Carlo910/ReHand-Project/Eagle/c.png

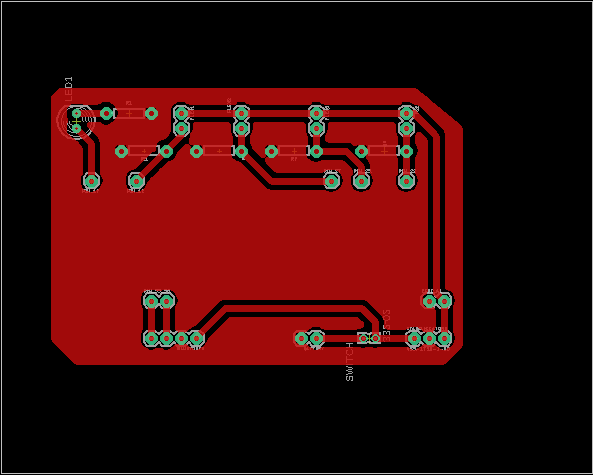
Eagle/c.png
