Carlo910/ReHand-Project/PYTHON/Immagini/indice_medio.png

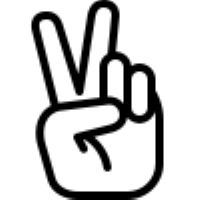
PYTHON/Immagini/indice_medio.png
