Carlo910/ReHand-Project/PSOC/Project3.cydsn/codegentemp/UART_BT.c

/*******************************************************************************
* File Name: UART_BT.c
* Version 2.50
*
* Description:
*  This file provides all API functionality of the UART component
*
* Note:
*
********************************************************************************
* Copyright 2008-2015, Cypress Semiconductor Corporation.  All rights reserved.
* You may use this file only in accordance with the license, terms, conditions,
* disclaimers, and limitations in the end user license agreement accompanying
* the software package with which this file was provided.
*******************************************************************************/

#include "UART_BT.h"
#if (UART_BT_INTERNAL_CLOCK_USED)
    #include "UART_BT_IntClock.h"
#endif /* End UART_BT_INTERNAL_CLOCK_USED */


/***************************************
* Global data allocation
***************************************/

uint8 UART_BT_initVar = 0u;

#if (UART_BT_TX_INTERRUPT_ENABLED && UART_BT_TX_ENABLED)
    volatile uint8 UART_BT_txBuffer[UART_BT_TX_BUFFER_SIZE];
    volatile uint8 UART_BT_txBufferRead = 0u;
    uint8 UART_BT_txBufferWrite = 0u;
#endif /* (UART_BT_TX_INTERRUPT_ENABLED && UART_BT_TX_ENABLED) */

#if (UART_BT_RX_INTERRUPT_ENABLED && (UART_BT_RX_ENABLED || UART_BT_HD_ENABLED))
    uint8 UART_BT_errorStatus = 0u;
    volatile uint8 UART_BT_rxBuffer[UART_BT_RX_BUFFER_SIZE];
    volatile uint8 UART_BT_rxBufferRead  = 0u;
    volatile uint8 UART_BT_rxBufferWrite = 0u;
    volatile uint8 UART_BT_rxBufferLoopDetect = 0u;
    volatile uint8 UART_BT_rxBufferOverflow   = 0u;
    #if (UART_BT_RXHW_ADDRESS_ENABLED)
        volatile uint8 UART_BT_rxAddressMode = UART_BT_RX_ADDRESS_MODE;
        volatile uint8 UART_BT_rxAddressDetected = 0u;
    #endif /* (UART_BT_RXHW_ADDRESS_ENABLED) */
#endif /* (UART_BT_RX_INTERRUPT_ENABLED && (UART_BT_RX_ENABLED || UART_BT_HD_ENABLED)) */


/*******************************************************************************
* Function Name: UART_BT_Start
********************************************************************************
*
* Summary:
*  This is the preferred method to begin component operation.
*  UART_BT_Start() sets the initVar variable, calls the
*  UART_BT_Init() function, and then calls the
*  UART_BT_Enable() function.
*
* Parameters:
*  None.
*
* Return:
*  None.
*
* Global variables:
*  The UART_BT_intiVar variable is used to indicate initial
*  configuration of this component. The variable is initialized to zero (0u)
*  and set to one (1u) the first time UART_BT_Start() is called. This
*  allows for component initialization without re-initialization in all
*  subsequent calls to the UART_BT_Start() routine.
*
* Reentrant:
*  No.
*
*******************************************************************************/
void UART_BT_Start(void) 
{
    /* If not initialized then initialize all required hardware and software */
    if(UART_BT_initVar == 0u)
    {
        UART_BT_Init();
        UART_BT_initVar = 1u;
    }

    UART_BT_Enable();
}


/*******************************************************************************
* Function Name: UART_BT_Init
********************************************************************************
*
* Summary:
*  Initializes or restores the component according to the customizer Configure
*  dialog settings. It is not necessary to call UART_BT_Init() because
*  the UART_BT_Start() API calls this function and is the preferred
*  method to begin component operation.
*
* Parameters:
*  None.
*
* Return:
*  None.
*
*******************************************************************************/
void UART_BT_Init(void) 
{
    #if(UART_BT_RX_ENABLED || UART_BT_HD_ENABLED)

        #if (UART_BT_RX_INTERRUPT_ENABLED)
            /* Set RX interrupt vector and priority */
            (void) CyIntSetVector(UART_BT_RX_VECT_NUM, &UART_BT_RXISR);
            CyIntSetPriority(UART_BT_RX_VECT_NUM, UART_BT_RX_PRIOR_NUM);
            UART_BT_errorStatus = 0u;
        #endif /* (UART_BT_RX_INTERRUPT_ENABLED) */

        #if (UART_BT_RXHW_ADDRESS_ENABLED)
            UART_BT_SetRxAddressMode(UART_BT_RX_ADDRESS_MODE);
            UART_BT_SetRxAddress1(UART_BT_RX_HW_ADDRESS1);
            UART_BT_SetRxAddress2(UART_BT_RX_HW_ADDRESS2);
        #endif /* End UART_BT_RXHW_ADDRESS_ENABLED */

        /* Init Count7 period */
        UART_BT_RXBITCTR_PERIOD_REG = UART_BT_RXBITCTR_INIT;
        /* Configure the Initial RX interrupt mask */
        UART_BT_RXSTATUS_MASK_REG  = UART_BT_INIT_RX_INTERRUPTS_MASK;
    #endif /* End UART_BT_RX_ENABLED || UART_BT_HD_ENABLED*/

    #if(UART_BT_TX_ENABLED)
        #if (UART_BT_TX_INTERRUPT_ENABLED)
            /* Set TX interrupt vector and priority */
            (void) CyIntSetVector(UART_BT_TX_VECT_NUM, &UART_BT_TXISR);
            CyIntSetPriority(UART_BT_TX_VECT_NUM, UART_BT_TX_PRIOR_NUM);
        #endif /* (UART_BT_TX_INTERRUPT_ENABLED) */

        /* Write Counter Value for TX Bit Clk Generator*/
        #if (UART_BT_TXCLKGEN_DP)
            UART_BT_TXBITCLKGEN_CTR_REG = UART_BT_BIT_CENTER;
            UART_BT_TXBITCLKTX_COMPLETE_REG = ((UART_BT_NUMBER_OF_DATA_BITS +
                        UART_BT_NUMBER_OF_START_BIT) * UART_BT_OVER_SAMPLE_COUNT) - 1u;
        #else
            UART_BT_TXBITCTR_PERIOD_REG = ((UART_BT_NUMBER_OF_DATA_BITS +
                        UART_BT_NUMBER_OF_START_BIT) * UART_BT_OVER_SAMPLE_8) - 1u;
        #endif /* End UART_BT_TXCLKGEN_DP */

        /* Configure the Initial TX interrupt mask */
        #if (UART_BT_TX_INTERRUPT_ENABLED)
            UART_BT_TXSTATUS_MASK_REG = UART_BT_TX_STS_FIFO_EMPTY;
        #else
            UART_BT_TXSTATUS_MASK_REG = UART_BT_INIT_TX_INTERRUPTS_MASK;
        #endif /*End UART_BT_TX_INTERRUPT_ENABLED*/

    #endif /* End UART_BT_TX_ENABLED */

    #if(UART_BT_PARITY_TYPE_SW)  /* Write Parity to Control Register */
        UART_BT_WriteControlRegister( \
            (UART_BT_ReadControlRegister() & (uint8)~UART_BT_CTRL_PARITY_TYPE_MASK) | \
            (uint8)(UART_BT_PARITY_TYPE << UART_BT_CTRL_PARITY_TYPE0_SHIFT) );
    #endif /* End UART_BT_PARITY_TYPE_SW */
}


/*******************************************************************************
* Function Name: UART_BT_Enable
********************************************************************************
*
* Summary:
*  Activates the hardware and begins component operation. It is not necessary
*  to call UART_BT_Enable() because the UART_BT_Start() API
*  calls this function, which is the preferred method to begin component
*  operation.

* Parameters:
*  None.
*
* Return:
*  None.
*
* Global Variables:
*  UART_BT_rxAddressDetected - set to initial state (0).
*
*******************************************************************************/
void UART_BT_Enable(void) 
{
    uint8 enableInterrupts;
    enableInterrupts = CyEnterCriticalSection();

    #if (UART_BT_RX_ENABLED || UART_BT_HD_ENABLED)
        /* RX Counter (Count7) Enable */
        UART_BT_RXBITCTR_CONTROL_REG |= UART_BT_CNTR_ENABLE;

        /* Enable the RX Interrupt */
        UART_BT_RXSTATUS_ACTL_REG  |= UART_BT_INT_ENABLE;

        #if (UART_BT_RX_INTERRUPT_ENABLED)
            UART_BT_EnableRxInt();

            #if (UART_BT_RXHW_ADDRESS_ENABLED)
                UART_BT_rxAddressDetected = 0u;
            #endif /* (UART_BT_RXHW_ADDRESS_ENABLED) */
        #endif /* (UART_BT_RX_INTERRUPT_ENABLED) */
    #endif /* (UART_BT_RX_ENABLED || UART_BT_HD_ENABLED) */

    #if(UART_BT_TX_ENABLED)
        /* TX Counter (DP/Count7) Enable */
        #if(!UART_BT_TXCLKGEN_DP)
            UART_BT_TXBITCTR_CONTROL_REG |= UART_BT_CNTR_ENABLE;
        #endif /* End UART_BT_TXCLKGEN_DP */

        /* Enable the TX Interrupt */
        UART_BT_TXSTATUS_ACTL_REG |= UART_BT_INT_ENABLE;
        #if (UART_BT_TX_INTERRUPT_ENABLED)
            UART_BT_ClearPendingTxInt(); /* Clear history of TX_NOT_EMPTY */
            UART_BT_EnableTxInt();
        #endif /* (UART_BT_TX_INTERRUPT_ENABLED) */
     #endif /* (UART_BT_TX_INTERRUPT_ENABLED) */

    #if (UART_BT_INTERNAL_CLOCK_USED)
        UART_BT_IntClock_Start();  /* Enable the clock */
    #endif /* (UART_BT_INTERNAL_CLOCK_USED) */

    CyExitCriticalSection(enableInterrupts);
}


/*******************************************************************************
* Function Name: UART_BT_Stop
********************************************************************************
*
* Summary:
*  Disables the UART operation.
*
* Parameters:
*  None.
*
* Return:
*  None.
*
*******************************************************************************/
void UART_BT_Stop(void) 
{
    uint8 enableInterrupts;
    enableInterrupts = CyEnterCriticalSection();

    /* Write Bit Counter Disable */
    #if (UART_BT_RX_ENABLED || UART_BT_HD_ENABLED)
        UART_BT_RXBITCTR_CONTROL_REG &= (uint8) ~UART_BT_CNTR_ENABLE;
    #endif /* (UART_BT_RX_ENABLED || UART_BT_HD_ENABLED) */

    #if (UART_BT_TX_ENABLED)
        #if(!UART_BT_TXCLKGEN_DP)
            UART_BT_TXBITCTR_CONTROL_REG &= (uint8) ~UART_BT_CNTR_ENABLE;
        #endif /* (!UART_BT_TXCLKGEN_DP) */
    #endif /* (UART_BT_TX_ENABLED) */

    #if (UART_BT_INTERNAL_CLOCK_USED)
        UART_BT_IntClock_Stop();   /* Disable the clock */
    #endif /* (UART_BT_INTERNAL_CLOCK_USED) */

    /* Disable internal interrupt component */
    #if (UART_BT_RX_ENABLED || UART_BT_HD_ENABLED)
        UART_BT_RXSTATUS_ACTL_REG  &= (uint8) ~UART_BT_INT_ENABLE;

        #if (UART_BT_RX_INTERRUPT_ENABLED)
            UART_BT_DisableRxInt();
        #endif /* (UART_BT_RX_INTERRUPT_ENABLED) */
    #endif /* (UART_BT_RX_ENABLED || UART_BT_HD_ENABLED) */

    #if (UART_BT_TX_ENABLED)
        UART_BT_TXSTATUS_ACTL_REG &= (uint8) ~UART_BT_INT_ENABLE;

        #if (UART_BT_TX_INTERRUPT_ENABLED)
            UART_BT_DisableTxInt();
        #endif /* (UART_BT_TX_INTERRUPT_ENABLED) */
    #endif /* (UART_BT_TX_ENABLED) */

    CyExitCriticalSection(enableInterrupts);
}


/*******************************************************************************
* Function Name: UART_BT_ReadControlRegister
********************************************************************************
*
* Summary:
*  Returns the current value of the control register.
*
* Parameters:
*  None.
*
* Return:
*  Contents of the control register.
*
*******************************************************************************/
uint8 UART_BT_ReadControlRegister(void) 
{
    #if (UART_BT_CONTROL_REG_REMOVED)
        return(0u);
    #else
        return(UART_BT_CONTROL_REG);
    #endif /* (UART_BT_CONTROL_REG_REMOVED) */
}


/*******************************************************************************
* Function Name: UART_BT_WriteControlRegister
********************************************************************************
*
* Summary:
*  Writes an 8-bit value into the control register
*
* Parameters:
*  control:  control register value
*
* Return:
*  None.
*
*******************************************************************************/
void  UART_BT_WriteControlRegister(uint8 control) 
{
    #if (UART_BT_CONTROL_REG_REMOVED)
        if(0u != control)
        {
            /* Suppress compiler warning */
        }
    #else
       UART_BT_CONTROL_REG = control;
    #endif /* (UART_BT_CONTROL_REG_REMOVED) */
}


#if(UART_BT_RX_ENABLED || UART_BT_HD_ENABLED)
    /*******************************************************************************
    * Function Name: UART_BT_SetRxInterruptMode
    ********************************************************************************
    *
    * Summary:
    *  Configures the RX interrupt sources enabled.
    *
    * Parameters:
    *  IntSrc:  Bit field containing the RX interrupts to enable. Based on the 
    *  bit-field arrangement of the status register. This value must be a 
    *  combination of status register bit-masks shown below:
    *      UART_BT_RX_STS_FIFO_NOTEMPTY    Interrupt on byte received.
    *      UART_BT_RX_STS_PAR_ERROR        Interrupt on parity error.
    *      UART_BT_RX_STS_STOP_ERROR       Interrupt on stop error.
    *      UART_BT_RX_STS_BREAK            Interrupt on break.
    *      UART_BT_RX_STS_OVERRUN          Interrupt on overrun error.
    *      UART_BT_RX_STS_ADDR_MATCH       Interrupt on address match.
    *      UART_BT_RX_STS_MRKSPC           Interrupt on address detect.
    *
    * Return:
    *  None.
    *
    * Theory:
    *  Enables the output of specific status bits to the interrupt controller
    *
    *******************************************************************************/
    void UART_BT_SetRxInterruptMode(uint8 intSrc) 
    {
        UART_BT_RXSTATUS_MASK_REG  = intSrc;
    }


    /*******************************************************************************
    * Function Name: UART_BT_ReadRxData
    ********************************************************************************
    *
    * Summary:
    *  Returns the next byte of received data. This function returns data without
    *  checking the status. You must check the status separately.
    *
    * Parameters:
    *  None.
    *
    * Return:
    *  Received data from RX register
    *
    * Global Variables:
    *  UART_BT_rxBuffer - RAM buffer pointer for save received data.
    *  UART_BT_rxBufferWrite - cyclic index for write to rxBuffer,
    *     checked to identify new data.
    *  UART_BT_rxBufferRead - cyclic index for read from rxBuffer,
    *     incremented after each byte has been read from buffer.
    *  UART_BT_rxBufferLoopDetect - cleared if loop condition was detected
    *     in RX ISR.
    *
    * Reentrant:
    *  No.
    *
    *******************************************************************************/
    uint8 UART_BT_ReadRxData(void) 
    {
        uint8 rxData;

    #if (UART_BT_RX_INTERRUPT_ENABLED)

        uint8 locRxBufferRead;
        uint8 locRxBufferWrite;

        /* Protect variables that could change on interrupt */
        UART_BT_DisableRxInt();

        locRxBufferRead  = UART_BT_rxBufferRead;
        locRxBufferWrite = UART_BT_rxBufferWrite;

        if( (UART_BT_rxBufferLoopDetect != 0u) || (locRxBufferRead != locRxBufferWrite) )
        {
            rxData = UART_BT_rxBuffer[locRxBufferRead];
            locRxBufferRead++;

            if(locRxBufferRead >= UART_BT_RX_BUFFER_SIZE)
            {
                locRxBufferRead = 0u;
            }
            /* Update the real pointer */
            UART_BT_rxBufferRead = locRxBufferRead;

            if(UART_BT_rxBufferLoopDetect != 0u)
            {
                UART_BT_rxBufferLoopDetect = 0u;
                #if ((UART_BT_RX_INTERRUPT_ENABLED) && (UART_BT_FLOW_CONTROL != 0u))
                    /* When Hardware Flow Control selected - return RX mask */
                    #if( UART_BT_HD_ENABLED )
                        if((UART_BT_CONTROL_REG & UART_BT_CTRL_HD_SEND) == 0u)
                        {   /* In Half duplex mode return RX mask only in RX
                            *  configuration set, otherwise
                            *  mask will be returned in LoadRxConfig() API.
                            */
                            UART_BT_RXSTATUS_MASK_REG  |= UART_BT_RX_STS_FIFO_NOTEMPTY;
                        }
                    #else
                        UART_BT_RXSTATUS_MASK_REG  |= UART_BT_RX_STS_FIFO_NOTEMPTY;
                    #endif /* end UART_BT_HD_ENABLED */
                #endif /* ((UART_BT_RX_INTERRUPT_ENABLED) && (UART_BT_FLOW_CONTROL != 0u)) */
            }
        }
        else
        {   /* Needs to check status for RX_STS_FIFO_NOTEMPTY bit */
            rxData = UART_BT_RXDATA_REG;
        }

        UART_BT_EnableRxInt();

    #else

        /* Needs to check status for RX_STS_FIFO_NOTEMPTY bit */
        rxData = UART_BT_RXDATA_REG;

    #endif /* (UART_BT_RX_INTERRUPT_ENABLED) */

        return(rxData);
    }


    /*******************************************************************************
    * Function Name: UART_BT_ReadRxStatus
    ********************************************************************************
    *
    * Summary:
    *  Returns the current state of the receiver status register and the software
    *  buffer overflow status.
    *
    * Parameters:
    *  None.
    *
    * Return:
    *  Current state of the status register.
    *
    * Side Effect:
    *  All status register bits are clear-on-read except
    *  UART_BT_RX_STS_FIFO_NOTEMPTY.
    *  UART_BT_RX_STS_FIFO_NOTEMPTY clears immediately after RX data
    *  register read.
    *
    * Global Variables:
    *  UART_BT_rxBufferOverflow - used to indicate overload condition.
    *   It set to one in RX interrupt when there isn't free space in
    *   UART_BT_rxBufferRead to write new data. This condition returned
    *   and cleared to zero by this API as an
    *   UART_BT_RX_STS_SOFT_BUFF_OVER bit along with RX Status register
    *   bits.
    *
    *******************************************************************************/
    uint8 UART_BT_ReadRxStatus(void) 
    {
        uint8 status;

        status = UART_BT_RXSTATUS_REG & UART_BT_RX_HW_MASK;

    #if (UART_BT_RX_INTERRUPT_ENABLED)
        if(UART_BT_rxBufferOverflow != 0u)
        {
            status |= UART_BT_RX_STS_SOFT_BUFF_OVER;
            UART_BT_rxBufferOverflow = 0u;
        }
    #endif /* (UART_BT_RX_INTERRUPT_ENABLED) */

        return(status);
    }


    /*******************************************************************************
    * Function Name: UART_BT_GetChar
    ********************************************************************************
    *
    * Summary:
    *  Returns the last received byte of data. UART_BT_GetChar() is
    *  designed for ASCII characters and returns a uint8 where 1 to 255 are values
    *  for valid characters and 0 indicates an error occurred or no data is present.
    *
    * Parameters:
    *  None.
    *
    * Return:
    *  Character read from UART RX buffer. ASCII characters from 1 to 255 are valid.
    *  A returned zero signifies an error condition or no data available.
    *
    * Global Variables:
    *  UART_BT_rxBuffer - RAM buffer pointer for save received data.
    *  UART_BT_rxBufferWrite - cyclic index for write to rxBuffer,
    *     checked to identify new data.
    *  UART_BT_rxBufferRead - cyclic index for read from rxBuffer,
    *     incremented after each byte has been read from buffer.
    *  UART_BT_rxBufferLoopDetect - cleared if loop condition was detected
    *     in RX ISR.
    *
    * Reentrant:
    *  No.
    *
    *******************************************************************************/
    uint8 UART_BT_GetChar(void) 
    {
        uint8 rxData = 0u;
        uint8 rxStatus;

    #if (UART_BT_RX_INTERRUPT_ENABLED)
        uint8 locRxBufferRead;
        uint8 locRxBufferWrite;

        /* Protect variables that could change on interrupt */
        UART_BT_DisableRxInt();

        locRxBufferRead  = UART_BT_rxBufferRead;
        locRxBufferWrite = UART_BT_rxBufferWrite;

        if( (UART_BT_rxBufferLoopDetect != 0u) || (locRxBufferRead != locRxBufferWrite) )
        {
            rxData = UART_BT_rxBuffer[locRxBufferRead];
            locRxBufferRead++;
            if(locRxBufferRead >= UART_BT_RX_BUFFER_SIZE)
            {
                locRxBufferRead = 0u;
            }
            /* Update the real pointer */
            UART_BT_rxBufferRead = locRxBufferRead;

            if(UART_BT_rxBufferLoopDetect != 0u)
            {
                UART_BT_rxBufferLoopDetect = 0u;
                #if( (UART_BT_RX_INTERRUPT_ENABLED) && (UART_BT_FLOW_CONTROL != 0u) )
                    /* When Hardware Flow Control selected - return RX mask */
                    #if( UART_BT_HD_ENABLED )
                        if((UART_BT_CONTROL_REG & UART_BT_CTRL_HD_SEND) == 0u)
                        {   /* In Half duplex mode return RX mask only if
                            *  RX configuration set, otherwise
                            *  mask will be returned in LoadRxConfig() API.
                            */
                            UART_BT_RXSTATUS_MASK_REG |= UART_BT_RX_STS_FIFO_NOTEMPTY;
                        }
                    #else
                        UART_BT_RXSTATUS_MASK_REG |= UART_BT_RX_STS_FIFO_NOTEMPTY;
                    #endif /* end UART_BT_HD_ENABLED */
                #endif /* UART_BT_RX_INTERRUPT_ENABLED and Hardware flow control*/
            }

        }
        else
        {   rxStatus = UART_BT_RXSTATUS_REG;
            if((rxStatus & UART_BT_RX_STS_FIFO_NOTEMPTY) != 0u)
            {   /* Read received data from FIFO */
                rxData = UART_BT_RXDATA_REG;
                /*Check status on error*/
                if((rxStatus & (UART_BT_RX_STS_BREAK | UART_BT_RX_STS_PAR_ERROR |
                                UART_BT_RX_STS_STOP_ERROR | UART_BT_RX_STS_OVERRUN)) != 0u)
                {
                    rxData = 0u;
                }
            }
        }

        UART_BT_EnableRxInt();

    #else

        rxStatus =UART_BT_RXSTATUS_REG;
        if((rxStatus & UART_BT_RX_STS_FIFO_NOTEMPTY) != 0u)
        {
            /* Read received data from FIFO */
            rxData = UART_BT_RXDATA_REG;

            /*Check status on error*/
            if((rxStatus & (UART_BT_RX_STS_BREAK | UART_BT_RX_STS_PAR_ERROR |
                            UART_BT_RX_STS_STOP_ERROR | UART_BT_RX_STS_OVERRUN)) != 0u)
            {
                rxData = 0u;
            }
        }
    #endif /* (UART_BT_RX_INTERRUPT_ENABLED) */

        return(rxData);
    }


    /*******************************************************************************
    * Function Name: UART_BT_GetByte
    ********************************************************************************
    *
    * Summary:
    *  Reads UART RX buffer immediately, returns received character and error
    *  condition.
    *
    * Parameters:
    *  None.
    *
    * Return:
    *  MSB contains status and LSB contains UART RX data. If the MSB is nonzero,
    *  an error has occurred.
    *
    * Reentrant:
    *  No.
    *
    *******************************************************************************/
    uint16 UART_BT_GetByte(void) 
    {
        
    #if (UART_BT_RX_INTERRUPT_ENABLED)
        uint16 locErrorStatus;
        /* Protect variables that could change on interrupt */
        UART_BT_DisableRxInt();
        locErrorStatus = (uint16)UART_BT_errorStatus;
        UART_BT_errorStatus = 0u;
        UART_BT_EnableRxInt();
        return ( (uint16)(locErrorStatus << 8u) | UART_BT_ReadRxData() );
    #else
        return ( ((uint16)UART_BT_ReadRxStatus() << 8u) | UART_BT_ReadRxData() );
    #endif /* UART_BT_RX_INTERRUPT_ENABLED */
        
    }


    /*******************************************************************************
    * Function Name: UART_BT_GetRxBufferSize
    ********************************************************************************
    *
    * Summary:
    *  Returns the number of received bytes available in the RX buffer.
    *  * RX software buffer is disabled (RX Buffer Size parameter is equal to 4): 
    *    returns 0 for empty RX FIFO or 1 for not empty RX FIFO.
    *  * RX software buffer is enabled: returns the number of bytes available in 
    *    the RX software buffer. Bytes available in the RX FIFO do not take to 
    *    account.
    *
    * Parameters:
    *  None.
    *
    * Return:
    *  uint8: Number of bytes in the RX buffer. 
    *    Return value type depends on RX Buffer Size parameter.
    *
    * Global Variables:
    *  UART_BT_rxBufferWrite - used to calculate left bytes.
    *  UART_BT_rxBufferRead - used to calculate left bytes.
    *  UART_BT_rxBufferLoopDetect - checked to decide left bytes amount.
    *
    * Reentrant:
    *  No.
    *
    * Theory:
    *  Allows the user to find out how full the RX Buffer is.
    *
    *******************************************************************************/
    uint8 UART_BT_GetRxBufferSize(void)
                                                            
    {
        uint8 size;

    #if (UART_BT_RX_INTERRUPT_ENABLED)

        /* Protect variables that could change on interrupt */
        UART_BT_DisableRxInt();

        if(UART_BT_rxBufferRead == UART_BT_rxBufferWrite)
        {
            if(UART_BT_rxBufferLoopDetect != 0u)
            {
                size = UART_BT_RX_BUFFER_SIZE;
            }
            else
            {
                size = 0u;
            }
        }
        else if(UART_BT_rxBufferRead < UART_BT_rxBufferWrite)
        {
            size = (UART_BT_rxBufferWrite - UART_BT_rxBufferRead);
        }
        else
        {
            size = (UART_BT_RX_BUFFER_SIZE - UART_BT_rxBufferRead) + UART_BT_rxBufferWrite;
        }

        UART_BT_EnableRxInt();

    #else

        /* We can only know if there is data in the fifo. */
        size = ((UART_BT_RXSTATUS_REG & UART_BT_RX_STS_FIFO_NOTEMPTY) != 0u) ? 1u : 0u;

    #endif /* (UART_BT_RX_INTERRUPT_ENABLED) */

        return(size);
    }


    /*******************************************************************************
    * Function Name: UART_BT_ClearRxBuffer
    ********************************************************************************
    *
    * Summary:
    *  Clears the receiver memory buffer and hardware RX FIFO of all received data.
    *
    * Parameters:
    *  None.
    *
    * Return:
    *  None.
    *
    * Global Variables:
    *  UART_BT_rxBufferWrite - cleared to zero.
    *  UART_BT_rxBufferRead - cleared to zero.
    *  UART_BT_rxBufferLoopDetect - cleared to zero.
    *  UART_BT_rxBufferOverflow - cleared to zero.
    *
    * Reentrant:
    *  No.
    *
    * Theory:
    *  Setting the pointers to zero makes the system believe there is no data to
    *  read and writing will resume at address 0 overwriting any data that may
    *  have remained in the RAM.
    *
    * Side Effects:
    *  Any received data not read from the RAM or FIFO buffer will be lost.
    *
    *******************************************************************************/
    void UART_BT_ClearRxBuffer(void) 
    {
        uint8 enableInterrupts;

        /* Clear the HW FIFO */
        enableInterrupts = CyEnterCriticalSection();
        UART_BT_RXDATA_AUX_CTL_REG |= (uint8)  UART_BT_RX_FIFO_CLR;
        UART_BT_RXDATA_AUX_CTL_REG &= (uint8) ~UART_BT_RX_FIFO_CLR;
        CyExitCriticalSection(enableInterrupts);

    #if (UART_BT_RX_INTERRUPT_ENABLED)

        /* Protect variables that could change on interrupt. */
        UART_BT_DisableRxInt();

        UART_BT_rxBufferRead = 0u;
        UART_BT_rxBufferWrite = 0u;
        UART_BT_rxBufferLoopDetect = 0u;
        UART_BT_rxBufferOverflow = 0u;

        UART_BT_EnableRxInt();

    #endif /* (UART_BT_RX_INTERRUPT_ENABLED) */

    }


    /*******************************************************************************
    * Function Name: UART_BT_SetRxAddressMode
    ********************************************************************************
    *
    * Summary:
    *  Sets the software controlled Addressing mode used by the RX portion of the
    *  UART.
    *
    * Parameters:
    *  addressMode: Enumerated value indicating the mode of RX addressing
    *  UART_BT__B_UART__AM_SW_BYTE_BYTE -  Software Byte-by-Byte address
    *                                               detection
    *  UART_BT__B_UART__AM_SW_DETECT_TO_BUFFER - Software Detect to Buffer
    *                                               address detection
    *  UART_BT__B_UART__AM_HW_BYTE_BY_BYTE - Hardware Byte-by-Byte address
    *                                               detection
    *  UART_BT__B_UART__AM_HW_DETECT_TO_BUFFER - Hardware Detect to Buffer
    *                                               address detection
    *  UART_BT__B_UART__AM_NONE - No address detection
    *
    * Return:
    *  None.
    *
    * Global Variables:
    *  UART_BT_rxAddressMode - the parameter stored in this variable for
    *   the farther usage in RX ISR.
    *  UART_BT_rxAddressDetected - set to initial state (0).
    *
    *******************************************************************************/
    void UART_BT_SetRxAddressMode(uint8 addressMode)
                                                        
    {
        #if(UART_BT_RXHW_ADDRESS_ENABLED)
            #if(UART_BT_CONTROL_REG_REMOVED)
                if(0u != addressMode)
                {
                    /* Suppress compiler warning */
                }
            #else /* UART_BT_CONTROL_REG_REMOVED */
                uint8 tmpCtrl;
                tmpCtrl = UART_BT_CONTROL_REG & (uint8)~UART_BT_CTRL_RXADDR_MODE_MASK;
                tmpCtrl |= (uint8)(addressMode << UART_BT_CTRL_RXADDR_MODE0_SHIFT);
                UART_BT_CONTROL_REG = tmpCtrl;

                #if(UART_BT_RX_INTERRUPT_ENABLED && \
                   (UART_BT_RXBUFFERSIZE > UART_BT_FIFO_LENGTH) )
                    UART_BT_rxAddressMode = addressMode;
                    UART_BT_rxAddressDetected = 0u;
                #endif /* End UART_BT_RXBUFFERSIZE > UART_BT_FIFO_LENGTH*/
            #endif /* End UART_BT_CONTROL_REG_REMOVED */
        #else /* UART_BT_RXHW_ADDRESS_ENABLED */
            if(0u != addressMode)
            {
                /* Suppress compiler warning */
            }
        #endif /* End UART_BT_RXHW_ADDRESS_ENABLED */
    }


    /*******************************************************************************
    * Function Name: UART_BT_SetRxAddress1
    ********************************************************************************
    *
    * Summary:
    *  Sets the first of two hardware-detectable receiver addresses.
    *
    * Parameters:
    *  address: Address #1 for hardware address detection.
    *
    * Return:
    *  None.
    *
    *******************************************************************************/
    void UART_BT_SetRxAddress1(uint8 address) 
    {
        UART_BT_RXADDRESS1_REG = address;
    }


    /*******************************************************************************
    * Function Name: UART_BT_SetRxAddress2
    ********************************************************************************
    *
    * Summary:
    *  Sets the second of two hardware-detectable receiver addresses.
    *
    * Parameters:
    *  address: Address #2 for hardware address detection.
    *
    * Return:
    *  None.
    *
    *******************************************************************************/
    void UART_BT_SetRxAddress2(uint8 address) 
    {
        UART_BT_RXADDRESS2_REG = address;
    }

#endif  /* UART_BT_RX_ENABLED || UART_BT_HD_ENABLED*/


#if( (UART_BT_TX_ENABLED) || (UART_BT_HD_ENABLED) )
    /*******************************************************************************
    * Function Name: UART_BT_SetTxInterruptMode
    ********************************************************************************
    *
    * Summary:
    *  Configures the TX interrupt sources to be enabled, but does not enable the
    *  interrupt.
    *
    * Parameters:
    *  intSrc: Bit field containing the TX interrupt sources to enable
    *   UART_BT_TX_STS_COMPLETE        Interrupt on TX byte complete
    *   UART_BT_TX_STS_FIFO_EMPTY      Interrupt when TX FIFO is empty
    *   UART_BT_TX_STS_FIFO_FULL       Interrupt when TX FIFO is full
    *   UART_BT_TX_STS_FIFO_NOT_FULL   Interrupt when TX FIFO is not full
    *
    * Return:
    *  None.
    *
    * Theory:
    *  Enables the output of specific status bits to the interrupt controller
    *
    *******************************************************************************/
    void UART_BT_SetTxInterruptMode(uint8 intSrc) 
    {
        UART_BT_TXSTATUS_MASK_REG = intSrc;
    }


    /*******************************************************************************
    * Function Name: UART_BT_WriteTxData
    ********************************************************************************
    *
    * Summary:
    *  Places a byte of data into the transmit buffer to be sent when the bus is
    *  available without checking the TX status register. You must check status
    *  separately.
    *
    * Parameters:
    *  txDataByte: data byte
    *
    * Return:
    * None.
    *
    * Global Variables:
    *  UART_BT_txBuffer - RAM buffer pointer for save data for transmission
    *  UART_BT_txBufferWrite - cyclic index for write to txBuffer,
    *    incremented after each byte saved to buffer.
    *  UART_BT_txBufferRead - cyclic index for read from txBuffer,
    *    checked to identify the condition to write to FIFO directly or to TX buffer
    *  UART_BT_initVar - checked to identify that the component has been
    *    initialized.
    *
    * Reentrant:
    *  No.
    *
    *******************************************************************************/
    void UART_BT_WriteTxData(uint8 txDataByte) 
    {
        /* If not Initialized then skip this function*/
        if(UART_BT_initVar != 0u)
        {
        #if (UART_BT_TX_INTERRUPT_ENABLED)

            /* Protect variables that could change on interrupt. */
            UART_BT_DisableTxInt();

            if( (UART_BT_txBufferRead == UART_BT_txBufferWrite) &&
                ((UART_BT_TXSTATUS_REG & UART_BT_TX_STS_FIFO_FULL) == 0u) )
            {
                /* Add directly to the FIFO. */
                UART_BT_TXDATA_REG = txDataByte;
            }
            else
            {
                if(UART_BT_txBufferWrite >= UART_BT_TX_BUFFER_SIZE)
                {
                    UART_BT_txBufferWrite = 0u;
                }

                UART_BT_txBuffer[UART_BT_txBufferWrite] = txDataByte;

                /* Add to the software buffer. */
                UART_BT_txBufferWrite++;
            }

            UART_BT_EnableTxInt();

        #else

            /* Add directly to the FIFO. */
            UART_BT_TXDATA_REG = txDataByte;

        #endif /*(UART_BT_TX_INTERRUPT_ENABLED) */
        }
    }


    /*******************************************************************************
    * Function Name: UART_BT_ReadTxStatus
    ********************************************************************************
    *
    * Summary:
    *  Reads the status register for the TX portion of the UART.
    *
    * Parameters:
    *  None.
    *
    * Return:
    *  Contents of the status register
    *
    * Theory:
    *  This function reads the TX status register, which is cleared on read.
    *  It is up to the user to handle all bits in this return value accordingly,
    *  even if the bit was not enabled as an interrupt source the event happened
    *  and must be handled accordingly.
    *
    *******************************************************************************/
    uint8 UART_BT_ReadTxStatus(void) 
    {
        return(UART_BT_TXSTATUS_REG);
    }


    /*******************************************************************************
    * Function Name: UART_BT_PutChar
    ********************************************************************************
    *
    * Summary:
    *  Puts a byte of data into the transmit buffer to be sent when the bus is
    *  available. This is a blocking API that waits until the TX buffer has room to
    *  hold the data.
    *
    * Parameters:
    *  txDataByte: Byte containing the data to transmit
    *
    * Return:
    *  None.
    *
    * Global Variables:
    *  UART_BT_txBuffer - RAM buffer pointer for save data for transmission
    *  UART_BT_txBufferWrite - cyclic index for write to txBuffer,
    *     checked to identify free space in txBuffer and incremented after each byte
    *     saved to buffer.
    *  UART_BT_txBufferRead - cyclic index for read from txBuffer,
    *     checked to identify free space in txBuffer.
    *  UART_BT_initVar - checked to identify that the component has been
    *     initialized.
    *
    * Reentrant:
    *  No.
    *
    * Theory:
    *  Allows the user to transmit any byte of data in a single transfer
    *
    *******************************************************************************/
    void UART_BT_PutChar(uint8 txDataByte) 
    {
    #if (UART_BT_TX_INTERRUPT_ENABLED)
        /* The temporary output pointer is used since it takes two instructions
        *  to increment with a wrap, and we can't risk doing that with the real
        *  pointer and getting an interrupt in between instructions.
        */
        uint8 locTxBufferWrite;
        uint8 locTxBufferRead;

        do
        { /* Block if software buffer is full, so we don't overwrite. */

        #if ((UART_BT_TX_BUFFER_SIZE > UART_BT_MAX_BYTE_VALUE) && (CY_PSOC3))
            /* Disable TX interrupt to protect variables from modification */
            UART_BT_DisableTxInt();
        #endif /* (UART_BT_TX_BUFFER_SIZE > UART_BT_MAX_BYTE_VALUE) && (CY_PSOC3) */

            locTxBufferWrite = UART_BT_txBufferWrite;
            locTxBufferRead  = UART_BT_txBufferRead;

        #if ((UART_BT_TX_BUFFER_SIZE > UART_BT_MAX_BYTE_VALUE) && (CY_PSOC3))
            /* Enable interrupt to continue transmission */
            UART_BT_EnableTxInt();
        #endif /* (UART_BT_TX_BUFFER_SIZE > UART_BT_MAX_BYTE_VALUE) && (CY_PSOC3) */
        }
        while( (locTxBufferWrite < locTxBufferRead) ? (locTxBufferWrite == (locTxBufferRead - 1u)) :
                                ((locTxBufferWrite - locTxBufferRead) ==
                                (uint8)(UART_BT_TX_BUFFER_SIZE - 1u)) );

        if( (locTxBufferRead == locTxBufferWrite) &&
            ((UART_BT_TXSTATUS_REG & UART_BT_TX_STS_FIFO_FULL) == 0u) )
        {
            /* Add directly to the FIFO */
            UART_BT_TXDATA_REG = txDataByte;
        }
        else
        {
            if(locTxBufferWrite >= UART_BT_TX_BUFFER_SIZE)
            {
                locTxBufferWrite = 0u;
            }
            /* Add to the software buffer. */
            UART_BT_txBuffer[locTxBufferWrite] = txDataByte;
            locTxBufferWrite++;

            /* Finally, update the real output pointer */
        #if ((UART_BT_TX_BUFFER_SIZE > UART_BT_MAX_BYTE_VALUE) && (CY_PSOC3))
            UART_BT_DisableTxInt();
        #endif /* (UART_BT_TX_BUFFER_SIZE > UART_BT_MAX_BYTE_VALUE) && (CY_PSOC3) */

            UART_BT_txBufferWrite = locTxBufferWrite;

        #if ((UART_BT_TX_BUFFER_SIZE > UART_BT_MAX_BYTE_VALUE) && (CY_PSOC3))
            UART_BT_EnableTxInt();
        #endif /* (UART_BT_TX_BUFFER_SIZE > UART_BT_MAX_BYTE_VALUE) && (CY_PSOC3) */

            if(0u != (UART_BT_TXSTATUS_REG & UART_BT_TX_STS_FIFO_EMPTY))
            {
                /* Trigger TX interrupt to send software buffer */
                UART_BT_SetPendingTxInt();
            }
        }

    #else

        while((UART_BT_TXSTATUS_REG & UART_BT_TX_STS_FIFO_FULL) != 0u)
        {
            /* Wait for room in the FIFO */
        }

        /* Add directly to the FIFO */
        UART_BT_TXDATA_REG = txDataByte;

    #endif /* UART_BT_TX_INTERRUPT_ENABLED */
    }


    /*******************************************************************************
    * Function Name: UART_BT_PutString
    ********************************************************************************
    *
    * Summary:
    *  Sends a NULL terminated string to the TX buffer for transmission.
    *
    * Parameters:
    *  string[]: Pointer to the null terminated string array residing in RAM or ROM
    *
    * Return:
    *  None.
    *
    * Global Variables:
    *  UART_BT_initVar - checked to identify that the component has been
    *     initialized.
    *
    * Reentrant:
    *  No.
    *
    * Theory:
    *  If there is not enough memory in the TX buffer for the entire string, this
    *  function blocks until the last character of the string is loaded into the
    *  TX buffer.
    *
    *******************************************************************************/
    void UART_BT_PutString(const char8 string[]) 
    {
        uint16 bufIndex = 0u;

        /* If not Initialized then skip this function */
        if(UART_BT_initVar != 0u)
        {
            /* This is a blocking function, it will not exit until all data is sent */
            while(string[bufIndex] != (char8) 0)
            {
                UART_BT_PutChar((uint8)string[bufIndex]);
                bufIndex++;
            }
        }
    }


    /*******************************************************************************
    * Function Name: UART_BT_PutArray
    ********************************************************************************
    *
    * Summary:
    *  Places N bytes of data from a memory array into the TX buffer for
    *  transmission.
    *
    * Parameters:
    *  string[]: Address of the memory array residing in RAM or ROM.
    *  byteCount: Number of bytes to be transmitted. The type depends on TX Buffer
    *             Size parameter.
    *
    * Return:
    *  None.
    *
    * Global Variables:
    *  UART_BT_initVar - checked to identify that the component has been
    *     initialized.
    *
    * Reentrant:
    *  No.
    *
    * Theory:
    *  If there is not enough memory in the TX buffer for the entire string, this
    *  function blocks until the last character of the string is loaded into the
    *  TX buffer.
    *
    *******************************************************************************/
    void UART_BT_PutArray(const uint8 string[], uint8 byteCount)
                                                                    
    {
        uint8 bufIndex = 0u;

        /* If not Initialized then skip this function */
        if(UART_BT_initVar != 0u)
        {
            while(bufIndex < byteCount)
            {
                UART_BT_PutChar(string[bufIndex]);
                bufIndex++;
            }
        }
    }


    /*******************************************************************************
    * Function Name: UART_BT_PutCRLF
    ********************************************************************************
    *
    * Summary:
    *  Writes a byte of data followed by a carriage return (0x0D) and line feed
    *  (0x0A) to the transmit buffer.
    *
    * Parameters:
    *  txDataByte: Data byte to transmit before the carriage return and line feed.
    *
    * Return:
    *  None.
    *
    * Global Variables:
    *  UART_BT_initVar - checked to identify that the component has been
    *     initialized.
    *
    * Reentrant:
    *  No.
    *
    *******************************************************************************/
    void UART_BT_PutCRLF(uint8 txDataByte) 
    {
        /* If not Initialized then skip this function */
        if(UART_BT_initVar != 0u)
        {
            UART_BT_PutChar(txDataByte);
            UART_BT_PutChar(0x0Du);
            UART_BT_PutChar(0x0Au);
        }
    }


    /*******************************************************************************
    * Function Name: UART_BT_GetTxBufferSize
    ********************************************************************************
    *
    * Summary:
    *  Returns the number of bytes in the TX buffer which are waiting to be 
    *  transmitted.
    *  * TX software buffer is disabled (TX Buffer Size parameter is equal to 4): 
    *    returns 0 for empty TX FIFO, 1 for not full TX FIFO or 4 for full TX FIFO.
    *  * TX software buffer is enabled: returns the number of bytes in the TX 
    *    software buffer which are waiting to be transmitted. Bytes available in the
    *    TX FIFO do not count.
    *
    * Parameters:
    *  None.
    *
    * Return:
    *  Number of bytes used in the TX buffer. Return value type depends on the TX 
    *  Buffer Size parameter.
    *
    * Global Variables:
    *  UART_BT_txBufferWrite - used to calculate left space.
    *  UART_BT_txBufferRead - used to calculate left space.
    *
    * Reentrant:
    *  No.
    *
    * Theory:
    *  Allows the user to find out how full the TX Buffer is.
    *
    *******************************************************************************/
    uint8 UART_BT_GetTxBufferSize(void)
                                                            
    {
        uint8 size;

    #if (UART_BT_TX_INTERRUPT_ENABLED)

        /* Protect variables that could change on interrupt. */
        UART_BT_DisableTxInt();

        if(UART_BT_txBufferRead == UART_BT_txBufferWrite)
        {
            size = 0u;
        }
        else if(UART_BT_txBufferRead < UART_BT_txBufferWrite)
        {
            size = (UART_BT_txBufferWrite - UART_BT_txBufferRead);
        }
        else
        {
            size = (UART_BT_TX_BUFFER_SIZE - UART_BT_txBufferRead) +
                    UART_BT_txBufferWrite;
        }

        UART_BT_EnableTxInt();

    #else

        size = UART_BT_TXSTATUS_REG;

        /* Is the fifo is full. */
        if((size & UART_BT_TX_STS_FIFO_FULL) != 0u)
        {
            size = UART_BT_FIFO_LENGTH;
        }
        else if((size & UART_BT_TX_STS_FIFO_EMPTY) != 0u)
        {
            size = 0u;
        }
        else
        {
            /* We only know there is data in the fifo. */
            size = 1u;
        }

    #endif /* (UART_BT_TX_INTERRUPT_ENABLED) */

    return(size);
    }


    /*******************************************************************************
    * Function Name: UART_BT_ClearTxBuffer
    ********************************************************************************
    *
    * Summary:
    *  Clears all data from the TX buffer and hardware TX FIFO.
    *
    * Parameters:
    *  None.
    *
    * Return:
    *  None.
    *
    * Global Variables:
    *  UART_BT_txBufferWrite - cleared to zero.
    *  UART_BT_txBufferRead - cleared to zero.
    *
    * Reentrant:
    *  No.
    *
    * Theory:
    *  Setting the pointers to zero makes the system believe there is no data to
    *  read and writing will resume at address 0 overwriting any data that may have
    *  remained in the RAM.
    *
    * Side Effects:
    *  Data waiting in the transmit buffer is not sent; a byte that is currently
    *  transmitting finishes transmitting.
    *
    *******************************************************************************/
    void UART_BT_ClearTxBuffer(void) 
    {
        uint8 enableInterrupts;

        enableInterrupts = CyEnterCriticalSection();
        /* Clear the HW FIFO */
        UART_BT_TXDATA_AUX_CTL_REG |= (uint8)  UART_BT_TX_FIFO_CLR;
        UART_BT_TXDATA_AUX_CTL_REG &= (uint8) ~UART_BT_TX_FIFO_CLR;
        CyExitCriticalSection(enableInterrupts);

    #if (UART_BT_TX_INTERRUPT_ENABLED)

        /* Protect variables that could change on interrupt. */
        UART_BT_DisableTxInt();

        UART_BT_txBufferRead = 0u;
        UART_BT_txBufferWrite = 0u;

        /* Enable Tx interrupt. */
        UART_BT_EnableTxInt();

    #endif /* (UART_BT_TX_INTERRUPT_ENABLED) */
    }


    /*******************************************************************************
    * Function Name: UART_BT_SendBreak
    ********************************************************************************
    *
    * Summary:
    *  Transmits a break signal on the bus.
    *
    * Parameters:
    *  uint8 retMode:  Send Break return mode. See the following table for options.
    *   UART_BT_SEND_BREAK - Initialize registers for break, send the Break
    *       signal and return immediately.
    *   UART_BT_WAIT_FOR_COMPLETE_REINIT - Wait until break transmission is
    *       complete, reinitialize registers to normal transmission mode then return
    *   UART_BT_REINIT - Reinitialize registers to normal transmission mode
    *       then return.
    *   UART_BT_SEND_WAIT_REINIT - Performs both options: 
    *      UART_BT_SEND_BREAK and UART_BT_WAIT_FOR_COMPLETE_REINIT.
    *      This option is recommended for most cases.
    *
    * Return:
    *  None.
    *
    * Global Variables:
    *  UART_BT_initVar - checked to identify that the component has been
    *     initialized.
    *  txPeriod - static variable, used for keeping TX period configuration.
    *
    * Reentrant:
    *  No.
    *
    * Theory:
    *  SendBreak function initializes registers to send 13-bit break signal. It is
    *  important to return the registers configuration to normal for continue 8-bit
    *  operation.
    *  There are 3 variants for this API usage:
    *  1) SendBreak(3) - function will send the Break signal and take care on the
    *     configuration returning. Function will block CPU until transmission
    *     complete.
    *  2) User may want to use blocking time if UART configured to the low speed
    *     operation
    *     Example for this case:
    *     SendBreak(0);     - initialize Break signal transmission
    *         Add your code here to use CPU time
    *     SendBreak(1);     - complete Break operation
    *  3) Same to 2) but user may want to initialize and use the interrupt to
    *     complete break operation.
    *     Example for this case:
    *     Initialize TX interrupt with "TX - On TX Complete" parameter
    *     SendBreak(0);     - initialize Break signal transmission
    *         Add your code here to use CPU time
    *     When interrupt appear with UART_BT_TX_STS_COMPLETE status:
    *     SendBreak(2);     - complete Break operation
    *
    * Side Effects:
    *  The UART_BT_SendBreak() function initializes registers to send a
    *  break signal.
    *  Break signal length depends on the break signal bits configuration.
    *  The register configuration should be reinitialized before normal 8-bit
    *  communication can continue.
    *
    *******************************************************************************/
    void UART_BT_SendBreak(uint8 retMode) 
    {

        /* If not Initialized then skip this function*/
        if(UART_BT_initVar != 0u)
        {
            /* Set the Counter to 13-bits and transmit a 00 byte */
            /* When that is done then reset the counter value back */
            uint8 tmpStat;

        #if(UART_BT_HD_ENABLED) /* Half Duplex mode*/

            if( (retMode == UART_BT_SEND_BREAK) ||
                (retMode == UART_BT_SEND_WAIT_REINIT ) )
            {
                /* CTRL_HD_SEND_BREAK - sends break bits in HD mode */
                UART_BT_WriteControlRegister(UART_BT_ReadControlRegister() |
                                                      UART_BT_CTRL_HD_SEND_BREAK);
                /* Send zeros */
                UART_BT_TXDATA_REG = 0u;

                do /* Wait until transmit starts */
                {
                    tmpStat = UART_BT_TXSTATUS_REG;
                }
                while((tmpStat & UART_BT_TX_STS_FIFO_EMPTY) != 0u);
            }

            if( (retMode == UART_BT_WAIT_FOR_COMPLETE_REINIT) ||
                (retMode == UART_BT_SEND_WAIT_REINIT) )
            {
                do /* Wait until transmit complete */
                {
                    tmpStat = UART_BT_TXSTATUS_REG;
                }
                while(((uint8)~tmpStat & UART_BT_TX_STS_COMPLETE) != 0u);
            }

            if( (retMode == UART_BT_WAIT_FOR_COMPLETE_REINIT) ||
                (retMode == UART_BT_REINIT) ||
                (retMode == UART_BT_SEND_WAIT_REINIT) )
            {
                UART_BT_WriteControlRegister(UART_BT_ReadControlRegister() &
                                              (uint8)~UART_BT_CTRL_HD_SEND_BREAK);
            }

        #else /* UART_BT_HD_ENABLED Full Duplex mode */

            static uint8 txPeriod;

            if( (retMode == UART_BT_SEND_BREAK) ||
                (retMode == UART_BT_SEND_WAIT_REINIT) )
            {
                /* CTRL_HD_SEND_BREAK - skip to send parity bit at Break signal in Full Duplex mode */
                #if( (UART_BT_PARITY_TYPE != UART_BT__B_UART__NONE_REVB) || \
                                    (UART_BT_PARITY_TYPE_SW != 0u) )
                    UART_BT_WriteControlRegister(UART_BT_ReadControlRegister() |
                                                          UART_BT_CTRL_HD_SEND_BREAK);
                #endif /* End UART_BT_PARITY_TYPE != UART_BT__B_UART__NONE_REVB  */

                #if(UART_BT_TXCLKGEN_DP)
                    txPeriod = UART_BT_TXBITCLKTX_COMPLETE_REG;
                    UART_BT_TXBITCLKTX_COMPLETE_REG = UART_BT_TXBITCTR_BREAKBITS;
                #else
                    txPeriod = UART_BT_TXBITCTR_PERIOD_REG;
                    UART_BT_TXBITCTR_PERIOD_REG = UART_BT_TXBITCTR_BREAKBITS8X;
                #endif /* End UART_BT_TXCLKGEN_DP */

                /* Send zeros */
                UART_BT_TXDATA_REG = 0u;

                do /* Wait until transmit starts */
                {
                    tmpStat = UART_BT_TXSTATUS_REG;
                }
                while((tmpStat & UART_BT_TX_STS_FIFO_EMPTY) != 0u);
            }

            if( (retMode == UART_BT_WAIT_FOR_COMPLETE_REINIT) ||
                (retMode == UART_BT_SEND_WAIT_REINIT) )
            {
                do /* Wait until transmit complete */
                {
                    tmpStat = UART_BT_TXSTATUS_REG;
                }
                while(((uint8)~tmpStat & UART_BT_TX_STS_COMPLETE) != 0u);
            }

            if( (retMode == UART_BT_WAIT_FOR_COMPLETE_REINIT) ||
                (retMode == UART_BT_REINIT) ||
                (retMode == UART_BT_SEND_WAIT_REINIT) )
            {

            #if(UART_BT_TXCLKGEN_DP)
                UART_BT_TXBITCLKTX_COMPLETE_REG = txPeriod;
            #else
                UART_BT_TXBITCTR_PERIOD_REG = txPeriod;
            #endif /* End UART_BT_TXCLKGEN_DP */

            #if( (UART_BT_PARITY_TYPE != UART_BT__B_UART__NONE_REVB) || \
                 (UART_BT_PARITY_TYPE_SW != 0u) )
                UART_BT_WriteControlRegister(UART_BT_ReadControlRegister() &
                                                      (uint8) ~UART_BT_CTRL_HD_SEND_BREAK);
            #endif /* End UART_BT_PARITY_TYPE != NONE */
            }
        #endif    /* End UART_BT_HD_ENABLED */
        }
    }


    /*******************************************************************************
    * Function Name: UART_BT_SetTxAddressMode
    ********************************************************************************
    *
    * Summary:
    *  Configures the transmitter to signal the next bytes is address or data.
    *
    * Parameters:
    *  addressMode: 
    *       UART_BT_SET_SPACE - Configure the transmitter to send the next
    *                                    byte as a data.
    *       UART_BT_SET_MARK  - Configure the transmitter to send the next
    *                                    byte as an address.
    *
    * Return:
    *  None.
    *
    * Side Effects:
    *  This function sets and clears UART_BT_CTRL_MARK bit in the Control
    *  register.
    *
    *******************************************************************************/
    void UART_BT_SetTxAddressMode(uint8 addressMode) 
    {
        /* Mark/Space sending enable */
        if(addressMode != 0u)
        {
        #if( UART_BT_CONTROL_REG_REMOVED == 0u )
            UART_BT_WriteControlRegister(UART_BT_ReadControlRegister() |
                                                  UART_BT_CTRL_MARK);
        #endif /* End UART_BT_CONTROL_REG_REMOVED == 0u */
        }
        else
        {
        #if( UART_BT_CONTROL_REG_REMOVED == 0u )
            UART_BT_WriteControlRegister(UART_BT_ReadControlRegister() &
                                                  (uint8) ~UART_BT_CTRL_MARK);
        #endif /* End UART_BT_CONTROL_REG_REMOVED == 0u */
        }
    }

#endif  /* EndUART_BT_TX_ENABLED */

#if(UART_BT_HD_ENABLED)


    /*******************************************************************************
    * Function Name: UART_BT_LoadRxConfig
    ********************************************************************************
    *
    * Summary:
    *  Loads the receiver configuration in half duplex mode. After calling this
    *  function, the UART is ready to receive data.
    *
    * Parameters:
    *  None.
    *
    * Return:
    *  None.
    *
    * Side Effects:
    *  Valid only in half duplex mode. You must make sure that the previous
    *  transaction is complete and it is safe to unload the transmitter
    *  configuration.
    *
    *******************************************************************************/
    void UART_BT_LoadRxConfig(void) 
    {
        UART_BT_WriteControlRegister(UART_BT_ReadControlRegister() &
                                                (uint8)~UART_BT_CTRL_HD_SEND);
        UART_BT_RXBITCTR_PERIOD_REG = UART_BT_HD_RXBITCTR_INIT;

    #if (UART_BT_RX_INTERRUPT_ENABLED)
        /* Enable RX interrupt after set RX configuration */
        UART_BT_SetRxInterruptMode(UART_BT_INIT_RX_INTERRUPTS_MASK);
    #endif /* (UART_BT_RX_INTERRUPT_ENABLED) */
    }


    /*******************************************************************************
    * Function Name: UART_BT_LoadTxConfig
    ********************************************************************************
    *
    * Summary:
    *  Loads the transmitter configuration in half duplex mode. After calling this
    *  function, the UART is ready to transmit data.
    *
    * Parameters:
    *  None.
    *
    * Return:
    *  None.
    *
    * Side Effects:
    *  Valid only in half duplex mode. You must make sure that the previous
    *  transaction is complete and it is safe to unload the receiver configuration.
    *
    *******************************************************************************/
    void UART_BT_LoadTxConfig(void) 
    {
    #if (UART_BT_RX_INTERRUPT_ENABLED)
        /* Disable RX interrupts before set TX configuration */
        UART_BT_SetRxInterruptMode(0u);
    #endif /* (UART_BT_RX_INTERRUPT_ENABLED) */

        UART_BT_WriteControlRegister(UART_BT_ReadControlRegister() | UART_BT_CTRL_HD_SEND);
        UART_BT_RXBITCTR_PERIOD_REG = UART_BT_HD_TXBITCTR_INIT;
    }

#endif  /* UART_BT_HD_ENABLED */


/* [] END OF FILE */
