Carlo910/ReHand-Project/PSOC/Project3.cydsn/codegentemp/UART_BT_INT.c

/*******************************************************************************
* File Name: UART_BTINT.c
* Version 2.50
*
* Description:
*  This file provides all Interrupt Service functionality of the UART component
*
********************************************************************************
* Copyright 2008-2015, Cypress Semiconductor Corporation.  All rights reserved.
* You may use this file only in accordance with the license, terms, conditions,
* disclaimers, and limitations in the end user license agreement accompanying
* the software package with which this file was provided.
*******************************************************************************/

#include "UART_BT.h"
#include "cyapicallbacks.h"


/***************************************
* Custom Declarations
***************************************/
/* `#START CUSTOM_DECLARATIONS` Place your declaration here */

/* `#END` */

#if (UART_BT_RX_INTERRUPT_ENABLED && (UART_BT_RX_ENABLED || UART_BT_HD_ENABLED))
    /*******************************************************************************
    * Function Name: UART_BT_RXISR
    ********************************************************************************
    *
    * Summary:
    *  Interrupt Service Routine for RX portion of the UART
    *
    * Parameters:
    *  None.
    *
    * Return:
    *  None.
    *
    * Global Variables:
    *  UART_BT_rxBuffer - RAM buffer pointer for save received data.
    *  UART_BT_rxBufferWrite - cyclic index for write to rxBuffer,
    *     increments after each byte saved to buffer.
    *  UART_BT_rxBufferRead - cyclic index for read from rxBuffer,
    *     checked to detect overflow condition.
    *  UART_BT_rxBufferOverflow - software overflow flag. Set to one
    *     when UART_BT_rxBufferWrite index overtakes
    *     UART_BT_rxBufferRead index.
    *  UART_BT_rxBufferLoopDetect - additional variable to detect overflow.
    *     Set to one when UART_BT_rxBufferWrite is equal to
    *    UART_BT_rxBufferRead
    *  UART_BT_rxAddressMode - this variable contains the Address mode,
    *     selected in customizer or set by UART_SetRxAddressMode() API.
    *  UART_BT_rxAddressDetected - set to 1 when correct address received,
    *     and analysed to store following addressed data bytes to the buffer.
    *     When not correct address received, set to 0 to skip following data bytes.
    *
    *******************************************************************************/
    CY_ISR(UART_BT_RXISR)
    {
        uint8 readData;
        uint8 readStatus;
        uint8 increment_pointer = 0u;

    #if(CY_PSOC3)
        uint8 int_en;
    #endif /* (CY_PSOC3) */

    #ifdef UART_BT_RXISR_ENTRY_CALLBACK
        UART_BT_RXISR_EntryCallback();
    #endif /* UART_BT_RXISR_ENTRY_CALLBACK */

        /* User code required at start of ISR */
        /* `#START UART_BT_RXISR_START` */

        /* `#END` */

    #if(CY_PSOC3)   /* Make sure nested interrupt is enabled */
        int_en = EA;
        CyGlobalIntEnable;
    #endif /* (CY_PSOC3) */

        do
        {
            /* Read receiver status register */
            readStatus = UART_BT_RXSTATUS_REG;
            /* Copy the same status to readData variable for backward compatibility support 
            *  of the user code in UART_BT_RXISR_ERROR` section. 
            */
            readData = readStatus;

            if((readStatus & (UART_BT_RX_STS_BREAK | 
                            UART_BT_RX_STS_PAR_ERROR |
                            UART_BT_RX_STS_STOP_ERROR | 
                            UART_BT_RX_STS_OVERRUN)) != 0u)
            {
                /* ERROR handling. */
                UART_BT_errorStatus |= readStatus & ( UART_BT_RX_STS_BREAK | 
                                                            UART_BT_RX_STS_PAR_ERROR | 
                                                            UART_BT_RX_STS_STOP_ERROR | 
                                                            UART_BT_RX_STS_OVERRUN);
                /* `#START UART_BT_RXISR_ERROR` */

                /* `#END` */
                
            #ifdef UART_BT_RXISR_ERROR_CALLBACK
                UART_BT_RXISR_ERROR_Callback();
            #endif /* UART_BT_RXISR_ERROR_CALLBACK */
            }
            
            if((readStatus & UART_BT_RX_STS_FIFO_NOTEMPTY) != 0u)
            {
                /* Read data from the RX data register */
                readData = UART_BT_RXDATA_REG;
            #if (UART_BT_RXHW_ADDRESS_ENABLED)
                if(UART_BT_rxAddressMode == (uint8)UART_BT__B_UART__AM_SW_DETECT_TO_BUFFER)
                {
                    if((readStatus & UART_BT_RX_STS_MRKSPC) != 0u)
                    {
                        if ((readStatus & UART_BT_RX_STS_ADDR_MATCH) != 0u)
                        {
                            UART_BT_rxAddressDetected = 1u;
                        }
                        else
                        {
                            UART_BT_rxAddressDetected = 0u;
                        }
                    }
                    if(UART_BT_rxAddressDetected != 0u)
                    {   /* Store only addressed data */
                        UART_BT_rxBuffer[UART_BT_rxBufferWrite] = readData;
                        increment_pointer = 1u;
                    }
                }
                else /* Without software addressing */
                {
                    UART_BT_rxBuffer[UART_BT_rxBufferWrite] = readData;
                    increment_pointer = 1u;
                }
            #else  /* Without addressing */
                UART_BT_rxBuffer[UART_BT_rxBufferWrite] = readData;
                increment_pointer = 1u;
            #endif /* (UART_BT_RXHW_ADDRESS_ENABLED) */

                /* Do not increment buffer pointer when skip not addressed data */
                if(increment_pointer != 0u)
                {
                    if(UART_BT_rxBufferLoopDetect != 0u)
                    {   /* Set Software Buffer status Overflow */
                        UART_BT_rxBufferOverflow = 1u;
                    }
                    /* Set next pointer. */
                    UART_BT_rxBufferWrite++;

                    /* Check pointer for a loop condition */
                    if(UART_BT_rxBufferWrite >= UART_BT_RX_BUFFER_SIZE)
                    {
                        UART_BT_rxBufferWrite = 0u;
                    }

                    /* Detect pre-overload condition and set flag */
                    if(UART_BT_rxBufferWrite == UART_BT_rxBufferRead)
                    {
                        UART_BT_rxBufferLoopDetect = 1u;
                        /* When Hardware Flow Control selected */
                        #if (UART_BT_FLOW_CONTROL != 0u)
                            /* Disable RX interrupt mask, it is enabled when user read data from the buffer using APIs */
                            UART_BT_RXSTATUS_MASK_REG  &= (uint8)~UART_BT_RX_STS_FIFO_NOTEMPTY;
                            CyIntClearPending(UART_BT_RX_VECT_NUM);
                            break; /* Break the reading of the FIFO loop, leave the data there for generating RTS signal */
                        #endif /* (UART_BT_FLOW_CONTROL != 0u) */
                    }
                }
            }
        }while((readStatus & UART_BT_RX_STS_FIFO_NOTEMPTY) != 0u);

        /* User code required at end of ISR (Optional) */
        /* `#START UART_BT_RXISR_END` */

        /* `#END` */

    #ifdef UART_BT_RXISR_EXIT_CALLBACK
        UART_BT_RXISR_ExitCallback();
    #endif /* UART_BT_RXISR_EXIT_CALLBACK */

    #if(CY_PSOC3)
        EA = int_en;
    #endif /* (CY_PSOC3) */
    }
    
#endif /* (UART_BT_RX_INTERRUPT_ENABLED && (UART_BT_RX_ENABLED || UART_BT_HD_ENABLED)) */


#if (UART_BT_TX_INTERRUPT_ENABLED && UART_BT_TX_ENABLED)
    /*******************************************************************************
    * Function Name: UART_BT_TXISR
    ********************************************************************************
    *
    * Summary:
    * Interrupt Service Routine for the TX portion of the UART
    *
    * Parameters:
    *  None.
    *
    * Return:
    *  None.
    *
    * Global Variables:
    *  UART_BT_txBuffer - RAM buffer pointer for transmit data from.
    *  UART_BT_txBufferRead - cyclic index for read and transmit data
    *     from txBuffer, increments after each transmitted byte.
    *  UART_BT_rxBufferWrite - cyclic index for write to txBuffer,
    *     checked to detect available for transmission bytes.
    *
    *******************************************************************************/
    CY_ISR(UART_BT_TXISR)
    {
    #if(CY_PSOC3)
        uint8 int_en;
    #endif /* (CY_PSOC3) */

    #ifdef UART_BT_TXISR_ENTRY_CALLBACK
        UART_BT_TXISR_EntryCallback();
    #endif /* UART_BT_TXISR_ENTRY_CALLBACK */

        /* User code required at start of ISR */
        /* `#START UART_BT_TXISR_START` */

        /* `#END` */

    #if(CY_PSOC3)   /* Make sure nested interrupt is enabled */
        int_en = EA;
        CyGlobalIntEnable;
    #endif /* (CY_PSOC3) */

        while((UART_BT_txBufferRead != UART_BT_txBufferWrite) &&
             ((UART_BT_TXSTATUS_REG & UART_BT_TX_STS_FIFO_FULL) == 0u))
        {
            /* Check pointer wrap around */
            if(UART_BT_txBufferRead >= UART_BT_TX_BUFFER_SIZE)
            {
                UART_BT_txBufferRead = 0u;
            }

            UART_BT_TXDATA_REG = UART_BT_txBuffer[UART_BT_txBufferRead];

            /* Set next pointer */
            UART_BT_txBufferRead++;
        }

        /* User code required at end of ISR (Optional) */
        /* `#START UART_BT_TXISR_END` */

        /* `#END` */

    #ifdef UART_BT_TXISR_EXIT_CALLBACK
        UART_BT_TXISR_ExitCallback();
    #endif /* UART_BT_TXISR_EXIT_CALLBACK */

    #if(CY_PSOC3)
        EA = int_en;
    #endif /* (CY_PSOC3) */
   }
#endif /* (UART_BT_TX_INTERRUPT_ENABLED && UART_BT_TX_ENABLED) */


/* [] END OF FILE */
