Carlo910/ReHand-Project/PSOC/Project3.cydsn/codegentemp/UART_BT_PM.c

/*******************************************************************************
* File Name: UART_BT_PM.c
* Version 2.50
*
* Description:
*  This file provides Sleep/WakeUp APIs functionality.
*
* Note:
*
********************************************************************************
* Copyright 2008-2015, Cypress Semiconductor Corporation.  All rights reserved.
* You may use this file only in accordance with the license, terms, conditions,
* disclaimers, and limitations in the end user license agreement accompanying
* the software package with which this file was provided.
*******************************************************************************/

#include "UART_BT.h"


/***************************************
* Local data allocation
***************************************/

static UART_BT_BACKUP_STRUCT  UART_BT_backup =
{
    /* enableState - disabled */
    0u,
};



/*******************************************************************************
* Function Name: UART_BT_SaveConfig
********************************************************************************
*
* Summary:
*  This function saves the component nonretention control register.
*  Does not save the FIFO which is a set of nonretention registers.
*  This function is called by the UART_BT_Sleep() function.
*
* Parameters:
*  None.
*
* Return:
*  None.
*
* Global Variables:
*  UART_BT_backup - modified when non-retention registers are saved.
*
* Reentrant:
*  No.
*
*******************************************************************************/
void UART_BT_SaveConfig(void)
{
    #if(UART_BT_CONTROL_REG_REMOVED == 0u)
        UART_BT_backup.cr = UART_BT_CONTROL_REG;
    #endif /* End UART_BT_CONTROL_REG_REMOVED */
}


/*******************************************************************************
* Function Name: UART_BT_RestoreConfig
********************************************************************************
*
* Summary:
*  Restores the nonretention control register except FIFO.
*  Does not restore the FIFO which is a set of nonretention registers.
*
* Parameters:
*  None.
*
* Return:
*  None.
*
* Global Variables:
*  UART_BT_backup - used when non-retention registers are restored.
*
* Reentrant:
*  No.
*
* Notes:
*  If this function is called without calling UART_BT_SaveConfig() 
*  first, the data loaded may be incorrect.
*
*******************************************************************************/
void UART_BT_RestoreConfig(void)
{
    #if(UART_BT_CONTROL_REG_REMOVED == 0u)
        UART_BT_CONTROL_REG = UART_BT_backup.cr;
    #endif /* End UART_BT_CONTROL_REG_REMOVED */
}


/*******************************************************************************
* Function Name: UART_BT_Sleep
********************************************************************************
*
* Summary:
*  This is the preferred API to prepare the component for sleep. 
*  The UART_BT_Sleep() API saves the current component state. Then it
*  calls the UART_BT_Stop() function and calls 
*  UART_BT_SaveConfig() to save the hardware configuration.
*  Call the UART_BT_Sleep() function before calling the CyPmSleep() 
*  or the CyPmHibernate() function. 
*
* Parameters:
*  None.
*
* Return:
*  None.
*
* Global Variables:
*  UART_BT_backup - modified when non-retention registers are saved.
*
* Reentrant:
*  No.
*
*******************************************************************************/
void UART_BT_Sleep(void)
{
    #if(UART_BT_RX_ENABLED || UART_BT_HD_ENABLED)
        if((UART_BT_RXSTATUS_ACTL_REG  & UART_BT_INT_ENABLE) != 0u)
        {
            UART_BT_backup.enableState = 1u;
        }
        else
        {
            UART_BT_backup.enableState = 0u;
        }
    #else
        if((UART_BT_TXSTATUS_ACTL_REG  & UART_BT_INT_ENABLE) !=0u)
        {
            UART_BT_backup.enableState = 1u;
        }
        else
        {
            UART_BT_backup.enableState = 0u;
        }
    #endif /* End UART_BT_RX_ENABLED || UART_BT_HD_ENABLED*/

    UART_BT_Stop();
    UART_BT_SaveConfig();
}


/*******************************************************************************
* Function Name: UART_BT_Wakeup
********************************************************************************
*
* Summary:
*  This is the preferred API to restore the component to the state when 
*  UART_BT_Sleep() was called. The UART_BT_Wakeup() function
*  calls the UART_BT_RestoreConfig() function to restore the 
*  configuration. If the component was enabled before the 
*  UART_BT_Sleep() function was called, the UART_BT_Wakeup()
*  function will also re-enable the component.
*
* Parameters:
*  None.
*
* Return:
*  None.
*
* Global Variables:
*  UART_BT_backup - used when non-retention registers are restored.
*
* Reentrant:
*  No.
*
*******************************************************************************/
void UART_BT_Wakeup(void)
{
    UART_BT_RestoreConfig();
    #if( (UART_BT_RX_ENABLED) || (UART_BT_HD_ENABLED) )
        UART_BT_ClearRxBuffer();
    #endif /* End (UART_BT_RX_ENABLED) || (UART_BT_HD_ENABLED) */
    #if(UART_BT_TX_ENABLED || UART_BT_HD_ENABLED)
        UART_BT_ClearTxBuffer();
    #endif /* End UART_BT_TX_ENABLED || UART_BT_HD_ENABLED */

    if(UART_BT_backup.enableState != 0u)
    {
        UART_BT_Enable();
    }
}


/* [] END OF FILE */
