Carlo910/ReHand-Project/PSOC/Project3.cydsn/codegentemp/ADC_DelSig_AMux.h

/*******************************************************************************
* File Name: ADC_DelSig_AMux.h
* Version 1.80
*
*  Description:
*    This file contains the constants and function prototypes for the Analog
*    Multiplexer User Module AMux.
*
*   Note:
*
********************************************************************************
* Copyright 2008-2010, Cypress Semiconductor Corporation.  All rights reserved.
* You may use this file only in accordance with the license, terms, conditions, 
* disclaimers, and limitations in the end user license agreement accompanying 
* the software package with which this file was provided.
********************************************************************************/

#if !defined(CY_AMUX_ADC_DelSig_AMux_H)
#define CY_AMUX_ADC_DelSig_AMux_H

#include "cyfitter.h"
#include "cyfitter_cfg.h"

#if ((CYDEV_CHIP_FAMILY_USED == CYDEV_CHIP_FAMILY_PSOC3) || \
         (CYDEV_CHIP_FAMILY_USED == CYDEV_CHIP_FAMILY_PSOC4) || \
         (CYDEV_CHIP_FAMILY_USED == CYDEV_CHIP_FAMILY_PSOC5))    
    #include "cytypes.h"
#else
    #include "syslib/cy_syslib.h"
#endif /* ((CYDEV_CHIP_FAMILY_USED == CYDEV_CHIP_FAMILY_PSOC3) */


/***************************************
*        Function Prototypes
***************************************/

void ADC_DelSig_AMux_Start(void) ;
#define ADC_DelSig_AMux_Init() ADC_DelSig_AMux_Start()
void ADC_DelSig_AMux_FastSelect(uint8 channel) ;
/* The Stop, Select, Connect, Disconnect and DisconnectAll functions are declared elsewhere */
/* void ADC_DelSig_AMux_Stop(void); */
/* void ADC_DelSig_AMux_Select(uint8 channel); */
/* void ADC_DelSig_AMux_Connect(uint8 channel); */
/* void ADC_DelSig_AMux_Disconnect(uint8 channel); */
/* void ADC_DelSig_AMux_DisconnectAll(void) */


/***************************************
*         Parameter Constants
***************************************/

#define ADC_DelSig_AMux_CHANNELS  2u
#define ADC_DelSig_AMux_MUXTYPE   1
#define ADC_DelSig_AMux_ATMOSTONE 0

/***************************************
*             API Constants
***************************************/

#define ADC_DelSig_AMux_NULL_CHANNEL 0xFFu
#define ADC_DelSig_AMux_MUX_SINGLE   1
#define ADC_DelSig_AMux_MUX_DIFF     2


/***************************************
*        Conditional Functions
***************************************/

#if ADC_DelSig_AMux_MUXTYPE == ADC_DelSig_AMux_MUX_SINGLE
# if !ADC_DelSig_AMux_ATMOSTONE
#  define ADC_DelSig_AMux_Connect(channel) ADC_DelSig_AMux_Set(channel)
# endif
# define ADC_DelSig_AMux_Disconnect(channel) ADC_DelSig_AMux_Unset(channel)
#else
# if !ADC_DelSig_AMux_ATMOSTONE
void ADC_DelSig_AMux_Connect(uint8 channel) ;
# endif
void ADC_DelSig_AMux_Disconnect(uint8 channel) ;
#endif

#if ADC_DelSig_AMux_ATMOSTONE
# define ADC_DelSig_AMux_Stop() ADC_DelSig_AMux_DisconnectAll()
# define ADC_DelSig_AMux_Select(channel) ADC_DelSig_AMux_FastSelect(channel)
void ADC_DelSig_AMux_DisconnectAll(void) ;
#else
# define ADC_DelSig_AMux_Stop() ADC_DelSig_AMux_Start()
void ADC_DelSig_AMux_Select(uint8 channel) ;
# define ADC_DelSig_AMux_DisconnectAll() ADC_DelSig_AMux_Start()
#endif

#endif /* CY_AMUX_ADC_DelSig_AMux_H */


/* [] END OF FILE */
