Carlo910/ReHand-Project/PSOC/Project3.cydsn/codegentemp/ADC_DelSig_PM.c

/*******************************************************************************
* File Name: ADC_DelSig_PM.c
* Version 3.30
*
* Description:
*  This file provides the power manager source code to the API for the
*  Delta-Sigma ADC Component.
*
* Note:
*
********************************************************************************
* Copyright 2008-2017, Cypress Semiconductor Corporation.  All rights reserved.
* You may use this file only in accordance with the license, terms, conditions,
* disclaimers, and limitations in the end user license agreement accompanying
* the software package with which this file was provided.
*******************************************************************************/

#include "ADC_DelSig.h"

static ADC_DelSig_BACKUP_STRUCT ADC_DelSig_backup =
{
    ADC_DelSig_DISABLED,
    ADC_DelSig_CFG1_DEC_CR
};


/*******************************************************************************
* Function Name: ADC_DelSig_SaveConfig
********************************************************************************
*
* Summary:
*  Save the register configuration which are not retention.
*
* Parameters:
*  None
*
* Return:
*  None
*
* Global variables:
*  ADC_DelSig_backup:  This global structure variable is used to store
*  configuration registers which are non retention whenever user wants to go
*  sleep mode by calling Sleep() API.
*
*******************************************************************************/
void ADC_DelSig_SaveConfig(void) 
{
    ADC_DelSig_backup.deccr = ADC_DelSig_DEC_CR_REG;
}


/*******************************************************************************
* Function Name: ADC_DelSig_RestoreConfig
********************************************************************************
*
* Summary:
*  Restore the register configurations which are not retention.
*
* Parameters:
*  None
*
* Return:
*  None
*
* Global variables:
*  ADC_DelSig_backup:  This global structure variable is used to restore
*  configuration registers which are non retention whenever user wants to switch
*  to active power mode by calling Wakeup() API.
*
*******************************************************************************/
void ADC_DelSig_RestoreConfig(void) 
{
    ADC_DelSig_DEC_CR_REG = ADC_DelSig_backup.deccr;
}


/*******************************************************************************
* Function Name: ADC_DelSig_Sleep
********************************************************************************
*
* Summary:
*  Stops the operation of the block and saves the user configuration.
*
* Parameters:
*  None
*
* Return:
*  None
*
* Global variables:
*  ADC_DelSig_backup:  The structure field 'enableState' is modified
*  depending on the enable state of the block before entering to sleep mode.
*
*******************************************************************************/
void ADC_DelSig_Sleep(void) 
{
    /* Save ADC enable state */
    if((ADC_DelSig_ACT_PWR_DEC_EN == (ADC_DelSig_PWRMGR_DEC_REG & ADC_DelSig_ACT_PWR_DEC_EN)) &&
       (ADC_DelSig_ACT_PWR_DSM_EN == (ADC_DelSig_PWRMGR_DSM_REG & ADC_DelSig_ACT_PWR_DSM_EN)))
    {
        /* Component is enabled */
        ADC_DelSig_backup.enableState = ADC_DelSig_ENABLED;
        if((ADC_DelSig_DEC_CR_REG & ADC_DelSig_DEC_START_CONV) != 0u)
        {   
            /* Conversion is started */
            ADC_DelSig_backup.enableState |= ADC_DelSig_STARTED;
        }
		
        /* Stop the configuration */
        ADC_DelSig_Stop();
    }
    else
    {
        /* Component is disabled */
        ADC_DelSig_backup.enableState = ADC_DelSig_DISABLED;
    }

    /* Save the user configuration */
    ADC_DelSig_SaveConfig();
}


/*******************************************************************************
* Function Name: ADC_DelSig_Wakeup
********************************************************************************
*
* Summary:
*  Restores the user configuration and enables the power to the block.
*
* Parameters:
*  None
*
* Return:
*  None
*
* Global variables:
*  ADC_DelSig_backup:  The structure field 'enableState' is used to
*  restore the enable state of block after wakeup from sleep mode.
*
*******************************************************************************/
void ADC_DelSig_Wakeup(void) 
{
    /* Restore the configuration */
    ADC_DelSig_RestoreConfig();

    /* Enables the component operation */
    if(ADC_DelSig_backup.enableState != ADC_DelSig_DISABLED)
    {
        ADC_DelSig_Enable();
        if((ADC_DelSig_backup.enableState & ADC_DelSig_STARTED) != 0u)
        {
            ADC_DelSig_StartConvert();
        }
    } /* Do nothing if component was disable before */
}


/* [] END OF FILE */
