Carlo910/ReHand-Project/PSOC/Project3.cydsn/codegentemp/Pin_BATT_aliases.h

/*******************************************************************************
* File Name: Pin_BATT.h  
* Version 2.20
*
* Description:
*  This file contains the Alias definitions for Per-Pin APIs in cypins.h. 
*  Information on using these APIs can be found in the System Reference Guide.
*
* Note:
*
********************************************************************************
* Copyright 2008-2015, Cypress Semiconductor Corporation.  All rights reserved.
* You may use this file only in accordance with the license, terms, conditions, 
* disclaimers, and limitations in the end user license agreement accompanying 
* the software package with which this file was provided.
*******************************************************************************/

#if !defined(CY_PINS_Pin_BATT_ALIASES_H) /* Pins Pin_BATT_ALIASES_H */
#define CY_PINS_Pin_BATT_ALIASES_H

#include "cytypes.h"
#include "cyfitter.h"


/***************************************
*              Constants        
***************************************/
#define Pin_BATT_0			(Pin_BATT__0__PC)
#define Pin_BATT_0_INTR	((uint16)((uint16)0x0001u << Pin_BATT__0__SHIFT))

#define Pin_BATT_INTR_ALL	 ((uint16)(Pin_BATT_0_INTR))

#endif /* End Pins Pin_BATT_ALIASES_H */


/* [] END OF FILE */
